pmajurski/16x8_LED_arduino_shield/Arduino_code/sprites.cpp

//
// Created by majurski on 5/31/2020.
//
#include "Arduino.h"

const uint8_t heart_beat1[16] PROGMEM = {
        0b00000000,
        0b00000000,
        0b01100110,
        0b01111110,
        0b01111110,
        0b00111100,
        0b00011000,
        0b00000000,
        0b00000000,
        0b00000000,
        0b01100110,
        0b01111110,
        0b01111110,
        0b00111100,
        0b00011000,
        0b00000000
};

const uint8_t heart_beat2[16] PROGMEM = {
        0b01100110,
        0b11111111,
        0b11111111,
        0b11111111,
        0b11111111,
        0b01111110,
        0b00111100,
        0b00011000,
        0b01100110,
        0b11111111,
        0b11111111,
        0b11111111,
        0b11111111,
        0b01111110,
        0b00111100,
        0b00011000
};

//originals
//const uint8_t heart_beat1[16] PROGMEM = {
//        0b00000000,
//        0b00101000,
//        0b01111100,
//        0b01111100,
//        0b00111000,
//        0b00010000,
//        0b00000000,
//        0b00000000,
//        0b00000000,
//        0b00101000,
//        0b01111100,
//        0b01111100,
//        0b00111000,
//        0b00010000,
//        0b00000000,
//        0b00000000
//};
//
//const uint8_t heart_beat2[16] PROGMEM = {
//        0b00000000,
//        0b01101100,
//        0b11111110,
//        0b11111110,
//        0b01111100,
//        0b00111000,
//        0b00010000,
//        0b00000000,
//        0b00000000,
//        0b01101100,
//        0b11111110,
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
        0b10000001,
        0b10100101,
        0b10000001,
        0b11111111,
        0b11011011,
        0b11111111,
        0b01111110,
        0b01111110,
        0b00111110,
        0b00011100,
        0b00001100,
        0b00000000,
        0b00000000,
        0b00000000
};
