pmajurski/16x8_LED_arduino_shield/Arduino_code/dwarfface.cpp

#include "dwarfface.h"
DwarfFace::DwarfFace() : DisplayProcess() {}

void DwarfFace::init() {
  deepCopyFrame(dwarfFace);
  updateDisplay();
}

void DwarfFace::run(DirectionInput::MoveDirection input) {}
